paulbetsch/TrueRandomNumberGenerator/TRNG_Pendel/Analyse/Pictures/DoppelPendel.png

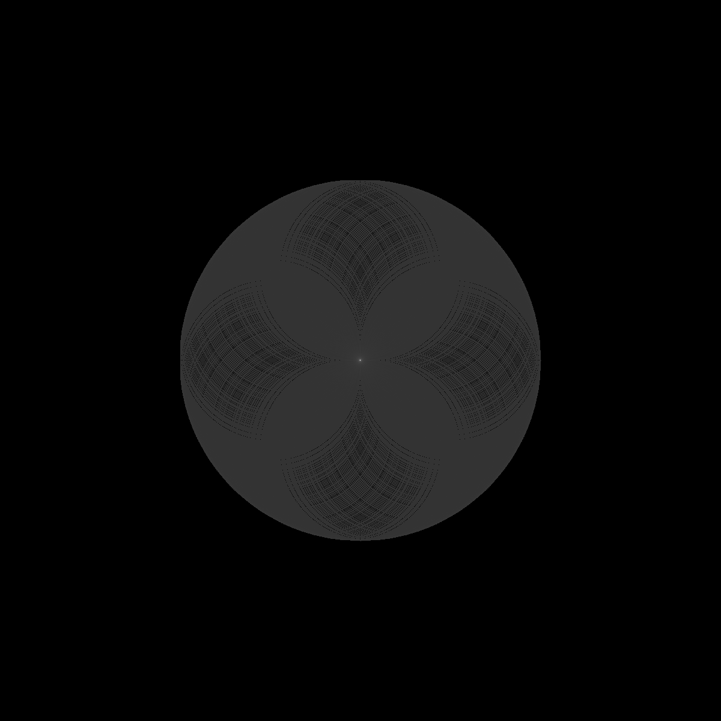
TRNG_Pendel/Analyse/Pictures/DoppelPendel.png
