paulbetsch/TrueRandomNumberGenerator/TRNG_Pendel/Analyse/Pictures/Pendel.png

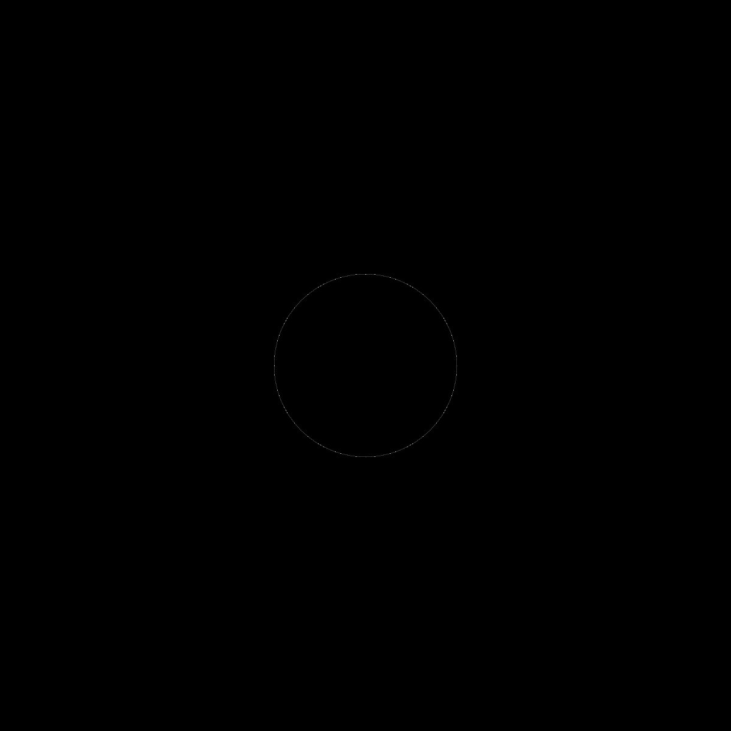
TRNG_Pendel/Analyse/Pictures/Pendel.png
