paulbetsch/TrueRandomNumberGenerator/TRNG_Pendel/Analyse/Pictures/TriPendel.png

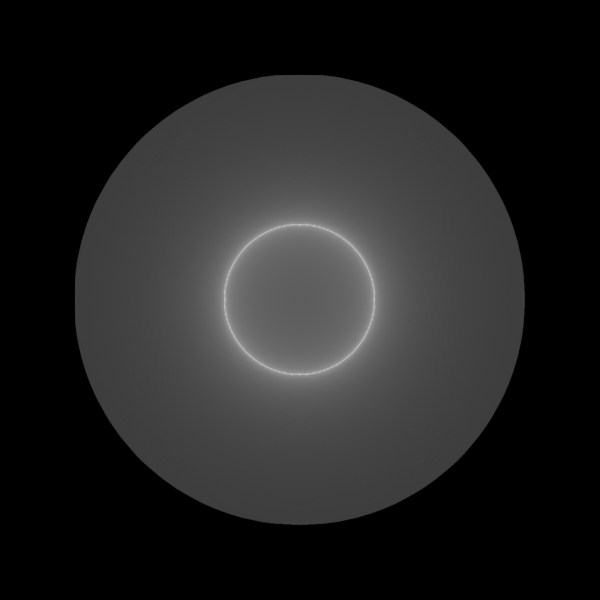
TRNG_Pendel/Analyse/Pictures/TriPendel.png
