paulbetsch/TrueRandomNumberGenerator/TRNG_Pendel/Ressources/Construction/Pictures/Image1.jpeg

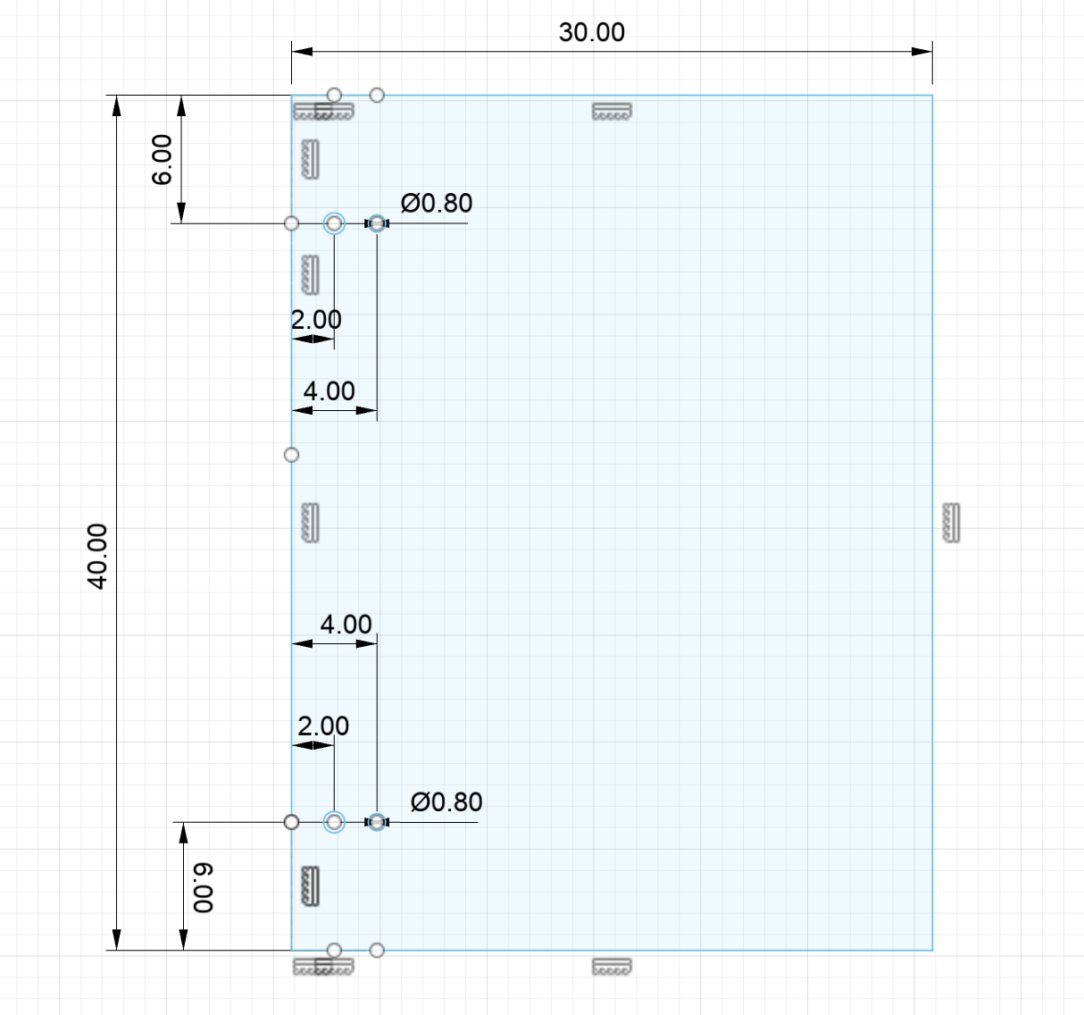
TRNG_Pendel/Ressources/Construction/Pictures/Image1.jpeg
