paulbetsch/TrueRandomNumberGenerator/TRNG_Pendel/Ressources/Construction/Pictures/Image7.jpeg

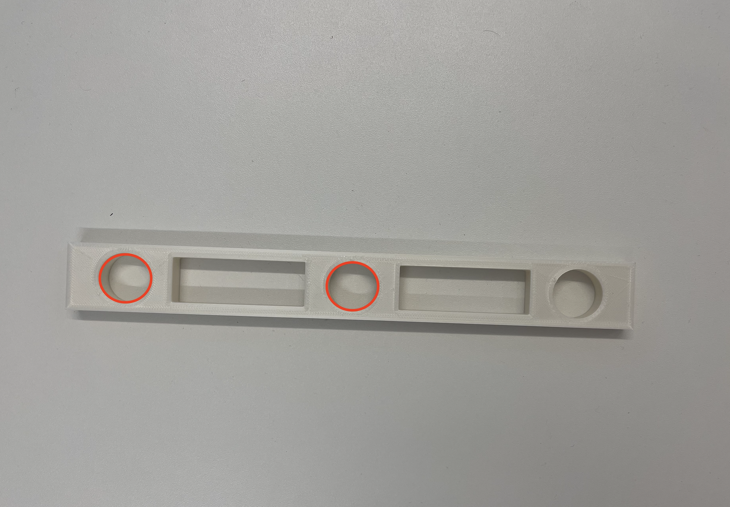
TRNG_Pendel/Ressources/Construction/Pictures/Image7.jpeg
