paulbetsch/TrueRandomNumberGenerator/TRNG_Pendel/Ressources/Construction/Pictures/Image8.jpeg

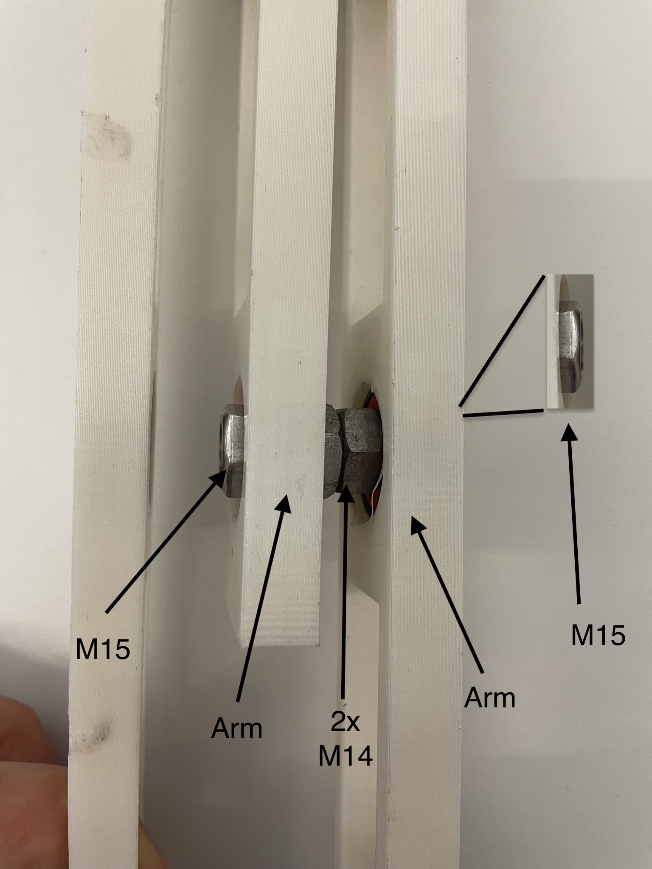
TRNG_Pendel/Ressources/Construction/Pictures/Image8.jpeg
