paulbetsch/TrueRandomNumberGenerator/TRNG_Pendel/Ressources/Construction/Pictures/Image9.jpeg

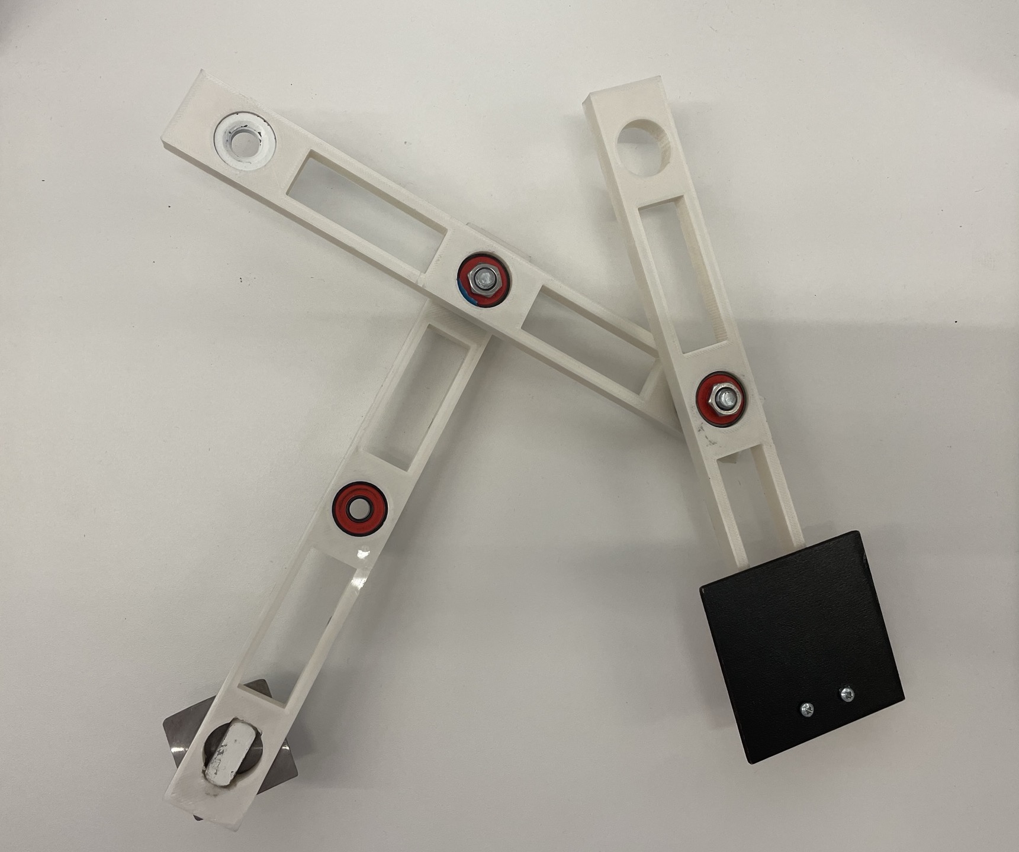
TRNG_Pendel/Ressources/Construction/Pictures/Image9.jpeg
