paulbetsch/TrueRandomNumberGenerator/TRNG_Pendel/Ressources/Construction/Pictures/Image11.jpeg

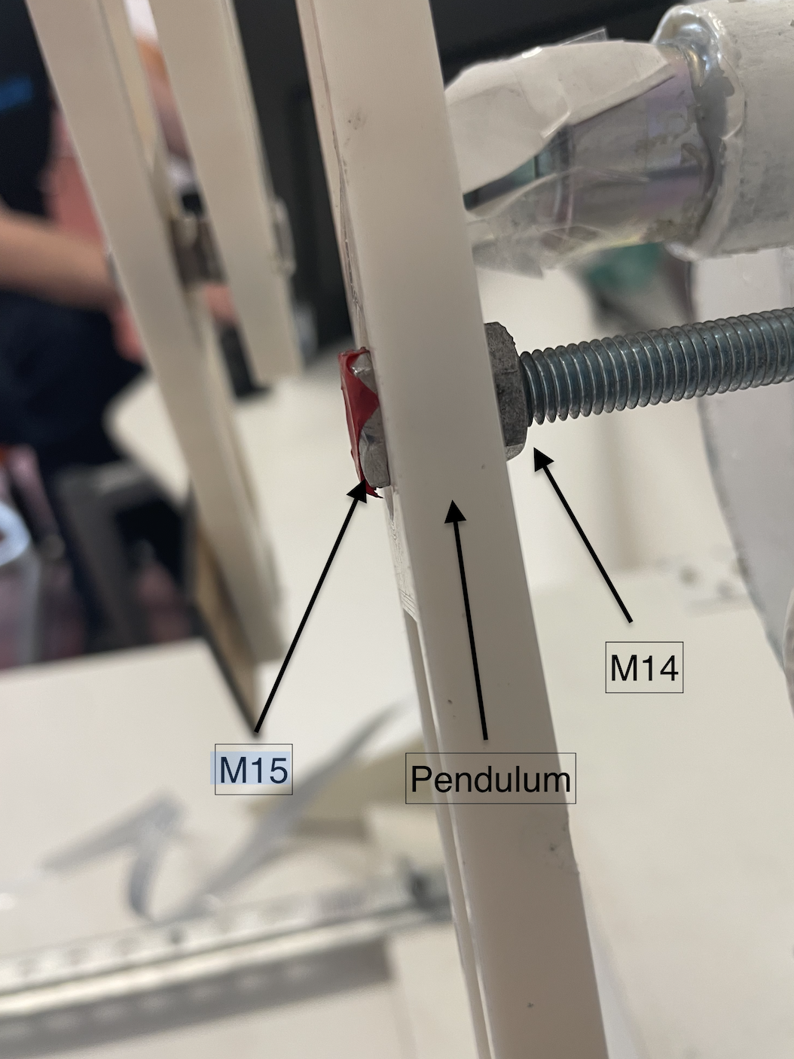
TRNG_Pendel/Ressources/Construction/Pictures/Image11.jpeg
