paulbetsch/TrueRandomNumberGenerator/TRNG_Pendel/Ressources/Construction/Pictures/Image13.jpeg

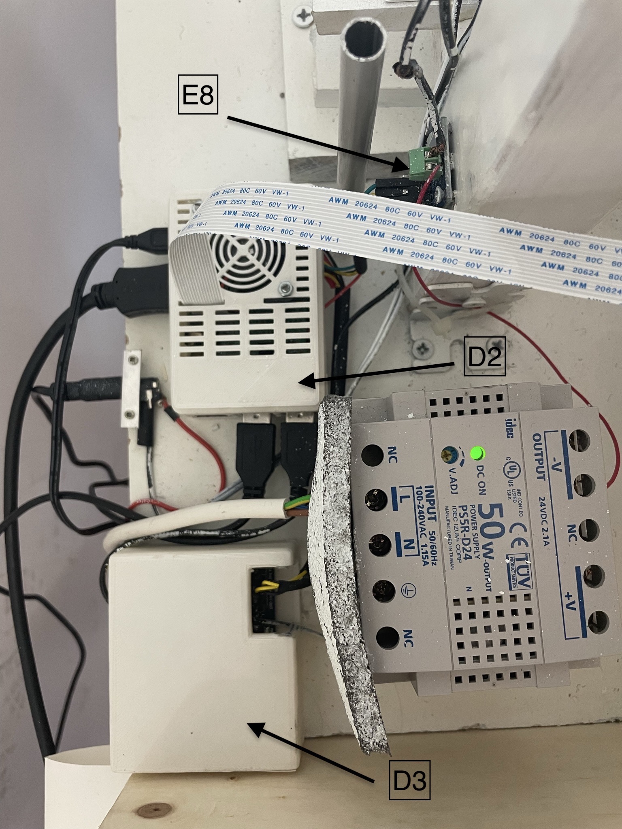
TRNG_Pendel/Ressources/Construction/Pictures/Image13.jpeg
