paulbetsch/TrueRandomNumberGenerator/TRNG_Pendel/Ressources/Construction/Pictures/Image15.jpeg

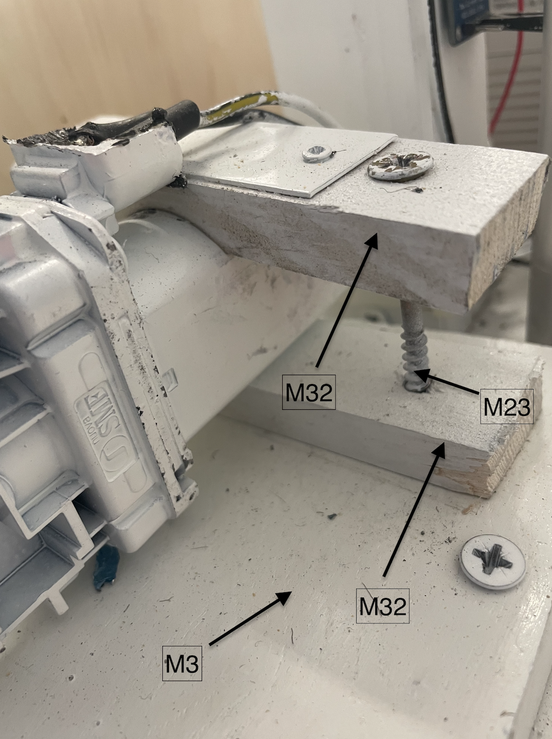
TRNG_Pendel/Ressources/Construction/Pictures/Image15.jpeg
