paulbetsch/TrueRandomNumberGenerator/TRNG_Pendel/Ressources/Construction/Pictures/Image16.jpeg

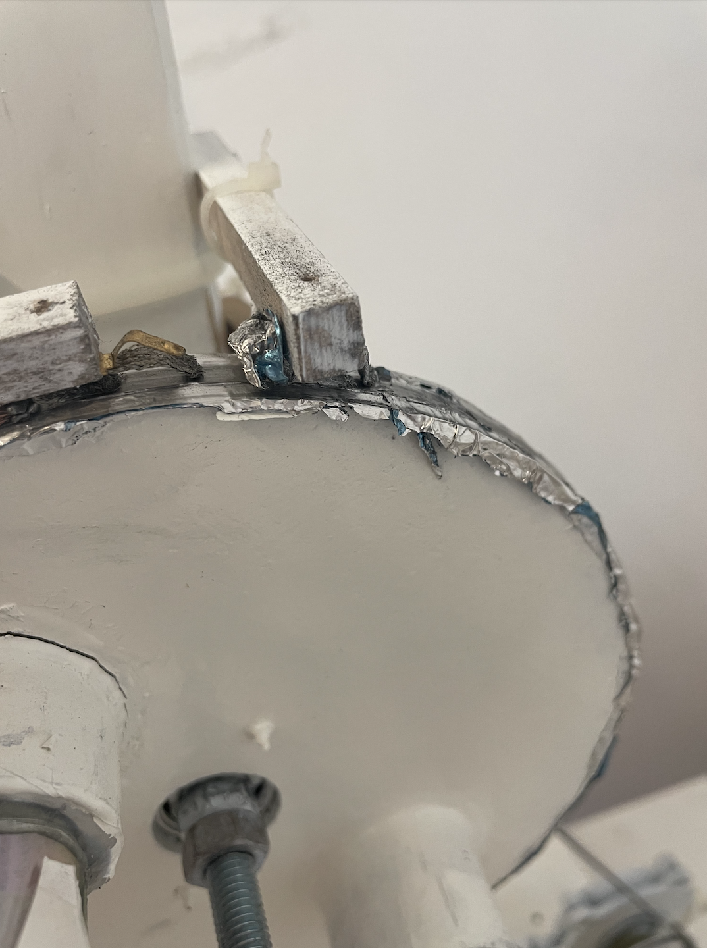
TRNG_Pendel/Ressources/Construction/Pictures/Image16.jpeg
