paulbetsch/TrueRandomNumberGenerator/TRNG_Pendel/Ressources/Construction/Pictures/Image17.jpeg

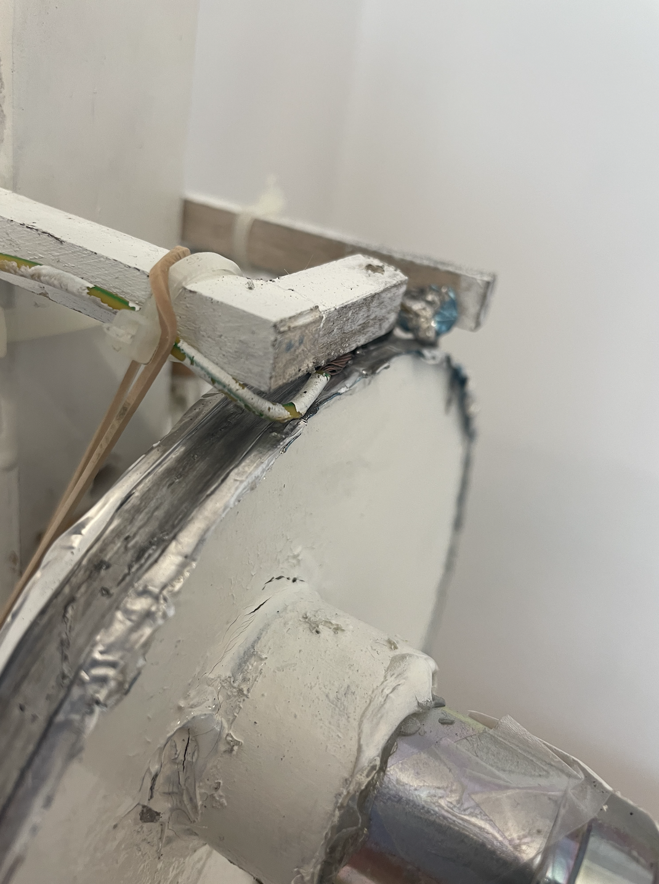
TRNG_Pendel/Ressources/Construction/Pictures/Image17.jpeg
