paulbetsch/TrueRandomNumberGenerator/TRNG_Pendel/Ressources/Construction/Pictures/Image19.jpeg

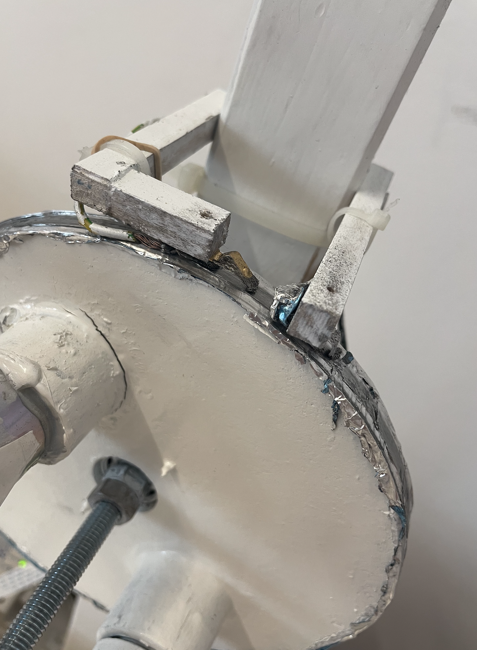
TRNG_Pendel/Ressources/Construction/Pictures/Image19.jpeg
