paulbetsch/TrueRandomNumberGenerator/TRNG_Pendel/Ressources/Construction/Pictures/Image21.jpeg

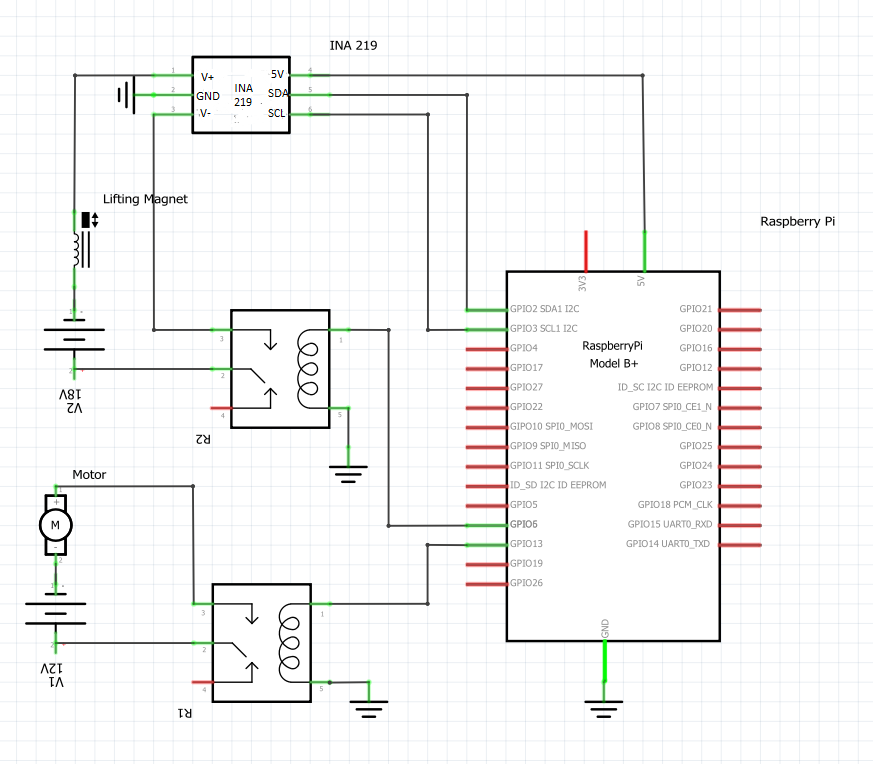
TRNG_Pendel/Ressources/Construction/Pictures/Image21.jpeg
