paulbetsch/TrueRandomNumberGenerator/TRNG_Pendel/Ressources/Construction/Pictures/Image22.jpeg

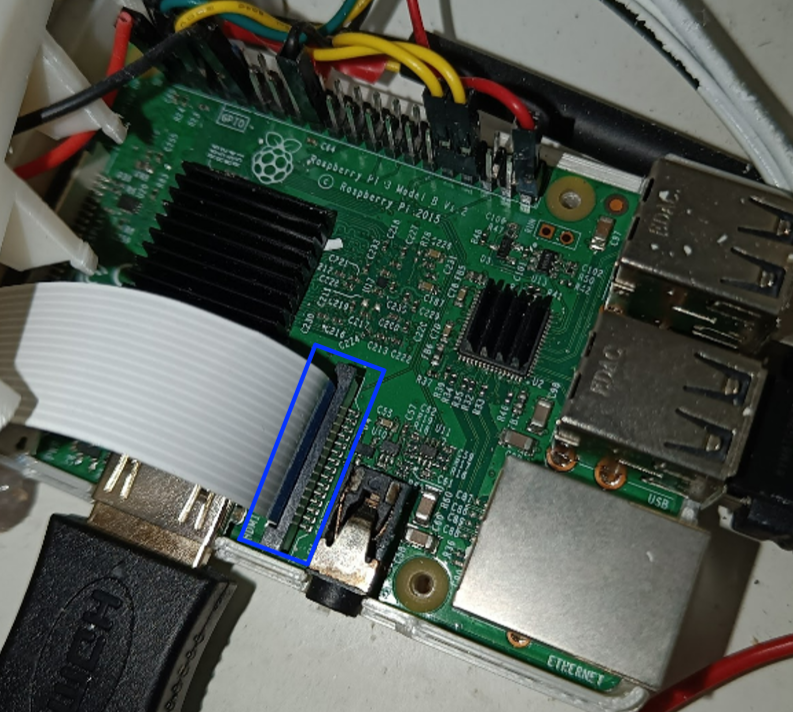
TRNG_Pendel/Ressources/Construction/Pictures/Image22.jpeg
