paulbetsch/TrueRandomNumberGenerator/TRNG_Pendel/Ressources/Construction/Pictures/Image23.jpeg

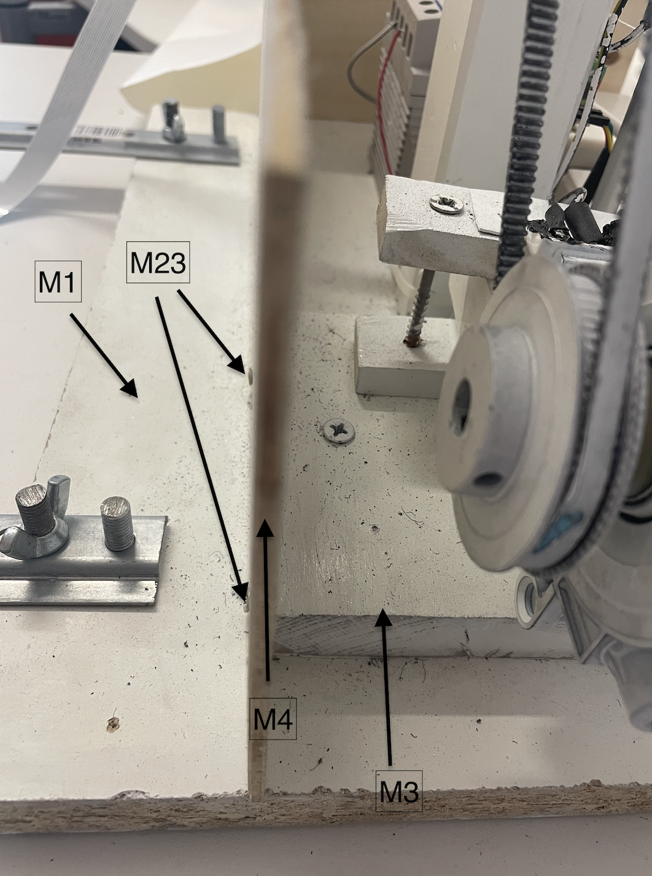
TRNG_Pendel/Ressources/Construction/Pictures/Image23.jpeg
