paulbetsch/TrueRandomNumberGenerator/TRNG_Pendel/Ressources/Construction/Pictures/Image25.jpeg

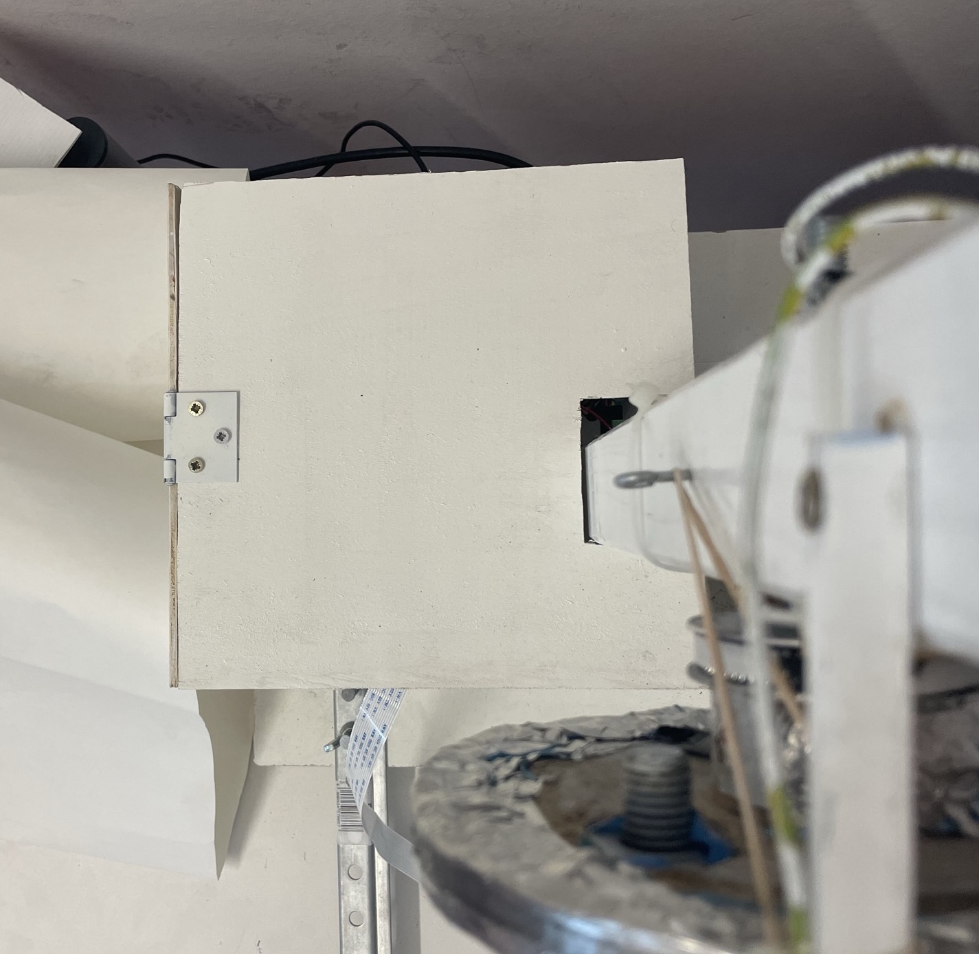
TRNG_Pendel/Ressources/Construction/Pictures/Image25.jpeg
